jkochavi/Fluid-Power-Controller/wiki_Support_Files/16bitMon.png

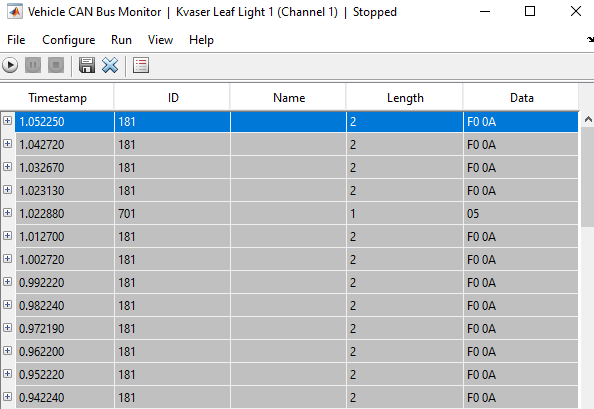
wiki_Support_Files/16bitMon.png
