jkochavi/Fluid-Power-Controller/wiki_Support_Files/16bitSend.png

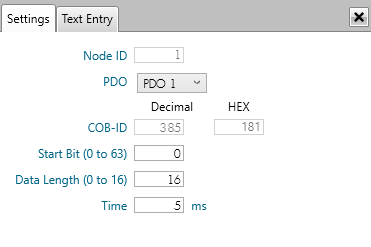
wiki_Support_Files/16bitSend.png
