jkochavi/Fluid-Power-Controller/wiki_Support_Files/CANopenframe.png

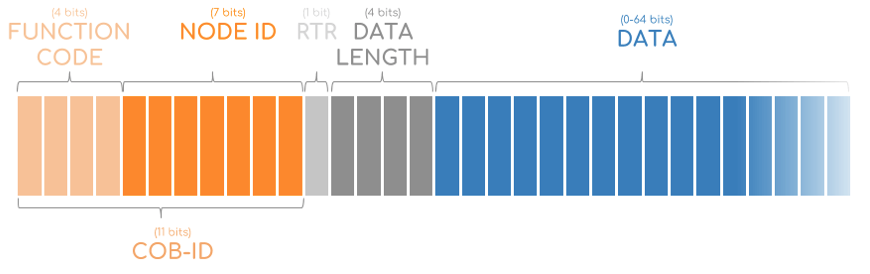
wiki_Support_Files/CANopenframe.png
