jkochavi/Fluid-Power-Controller/wiki_Support_Files/DB9.png

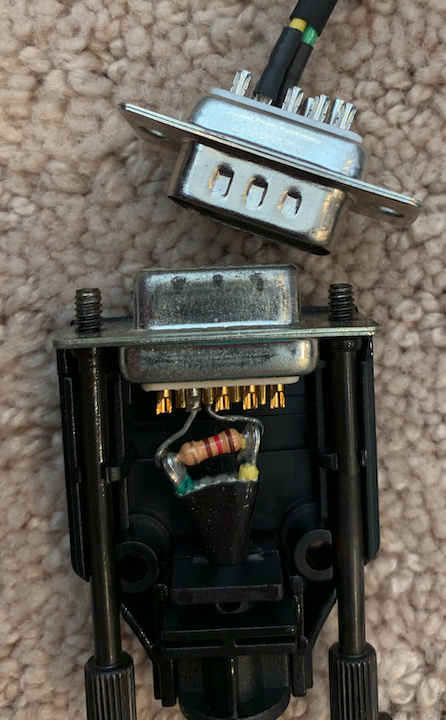
wiki_Support_Files/DB9.png
