jkochavi/Fluid-Power-Controller/wiki_Support_Files/dx.png

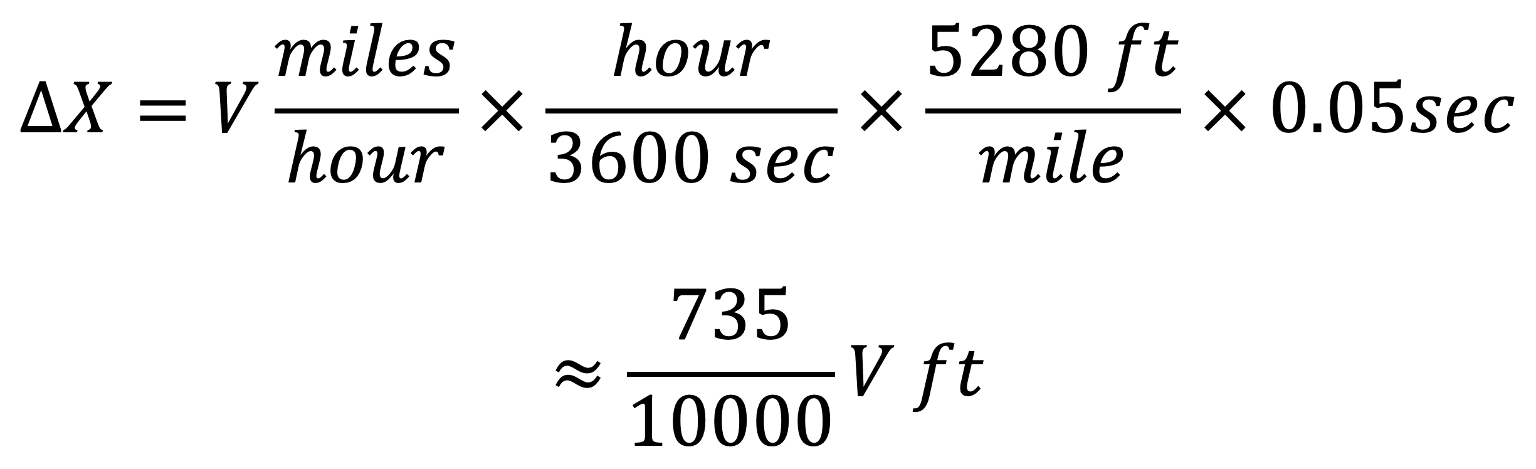
wiki_Support_Files/dx.png
