jkochavi/Fluid-Power-Controller/wiki_Support_Files/fig1.png

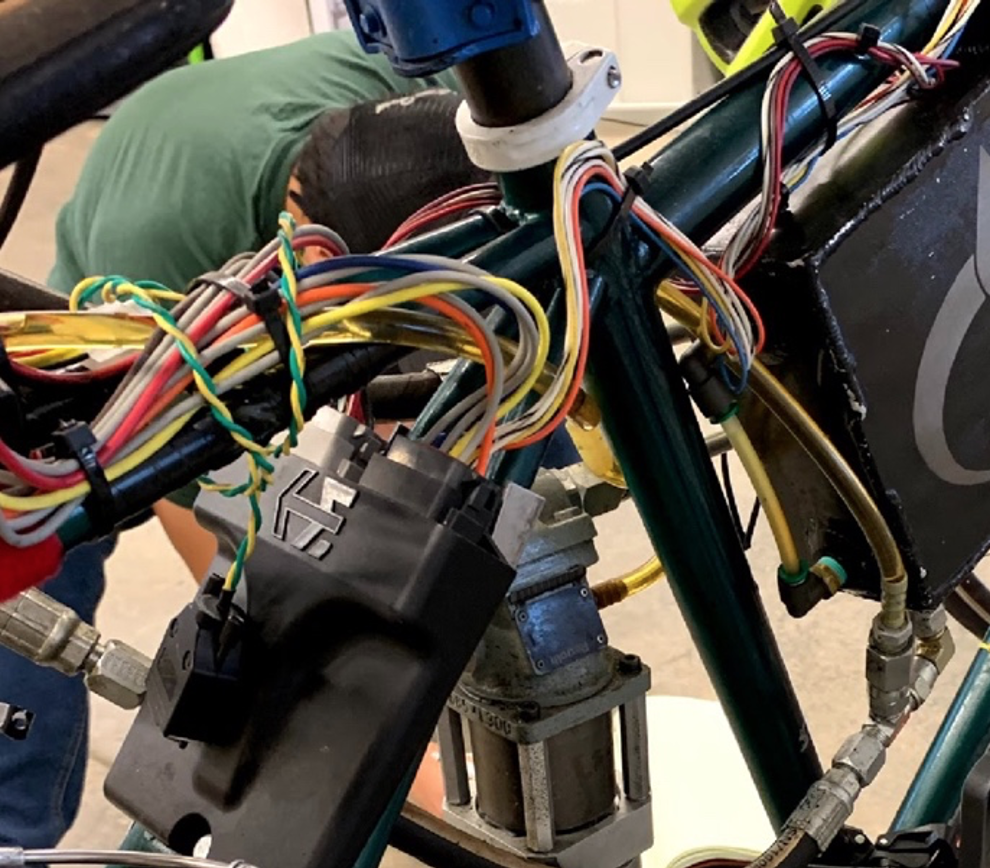
wiki_Support_Files/fig1.png
