jkochavi/Fluid-Power-Controller/wiki_Support_Files/fig2.png

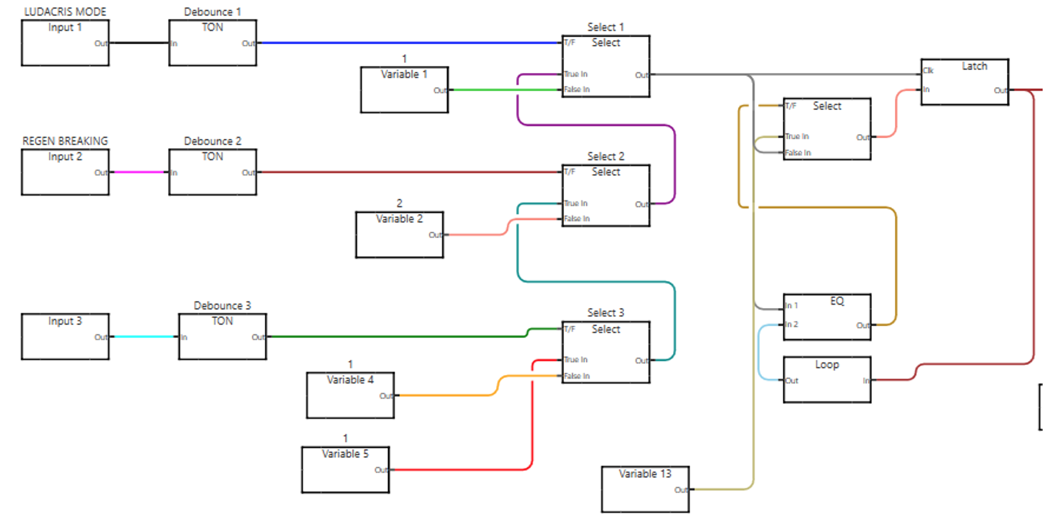
wiki_Support_Files/fig2.png
