jkochavi/Fluid-Power-Controller/wiki_Support_Files/fig3.png

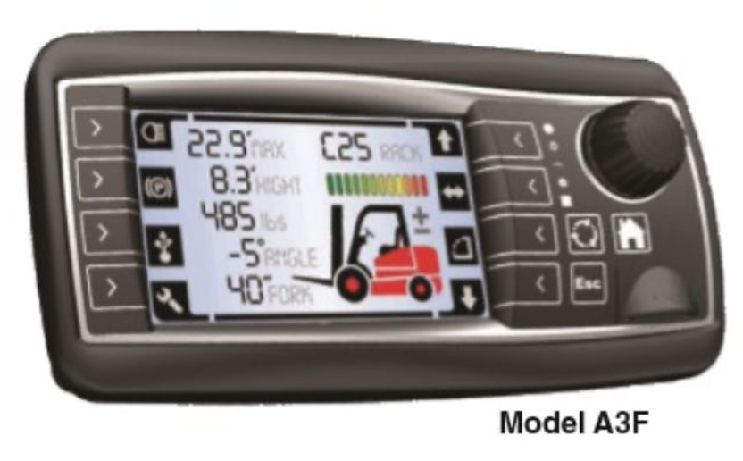
wiki_Support_Files/fig3.png
