jkochavi/Fluid-Power-Controller/wiki_Support_Files/fig4.png

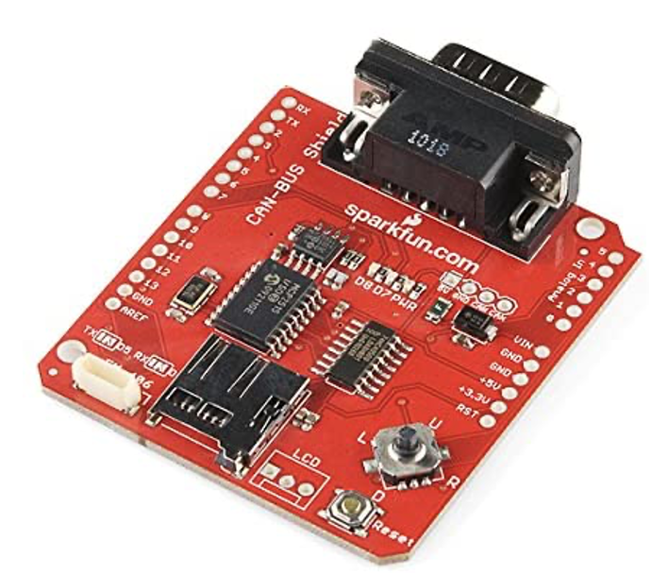
wiki_Support_Files/fig4.png
