jkochavi/Fluid-Power-Controller/wiki_Support_Files/fig5.png

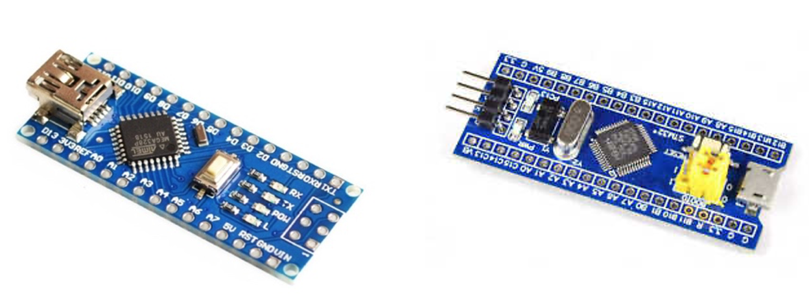
wiki_Support_Files/fig5.png
