jkochavi/Fluid-Power-Controller/wiki_Support_Files/fig6.png

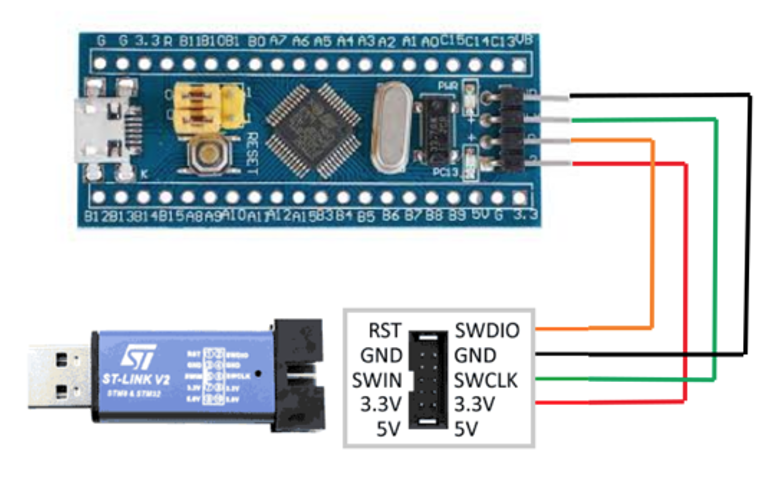
wiki_Support_Files/fig6.png
