jkochavi/Fluid-Power-Controller/wiki_Support_Files/fig7.png

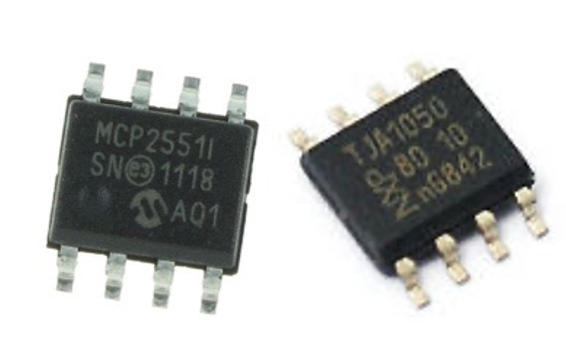
wiki_Support_Files/fig7.png
