jkochavi/Fluid-Power-Controller/wiki_Support_Files/fig8.png

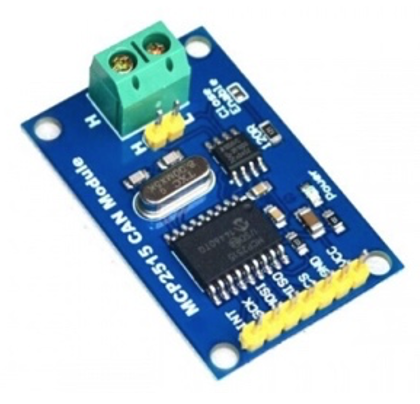
wiki_Support_Files/fig8.png
