jkochavi/Fluid-Power-Controller/wiki_Support_Files/fig9.png

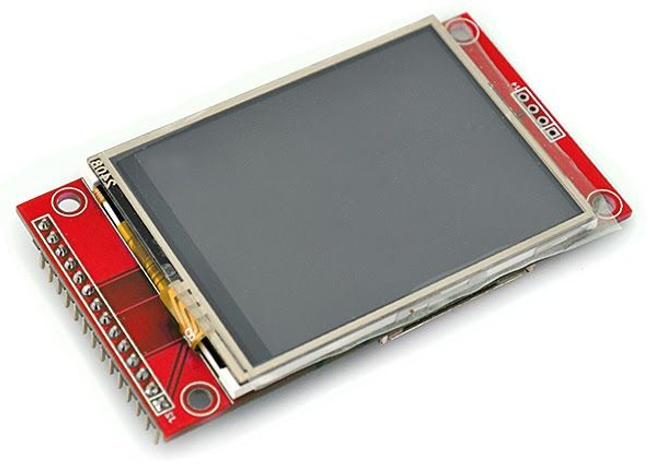
wiki_Support_Files/fig9.png
