jkochavi/Fluid-Power-Controller/wiki_Support_Files/fig10.png

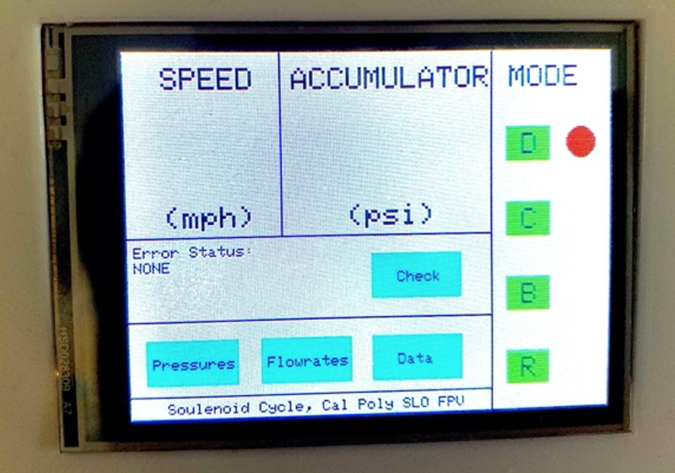
wiki_Support_Files/fig10.png
