jkochavi/Fluid-Power-Controller/wiki_Support_Files/fig11.png

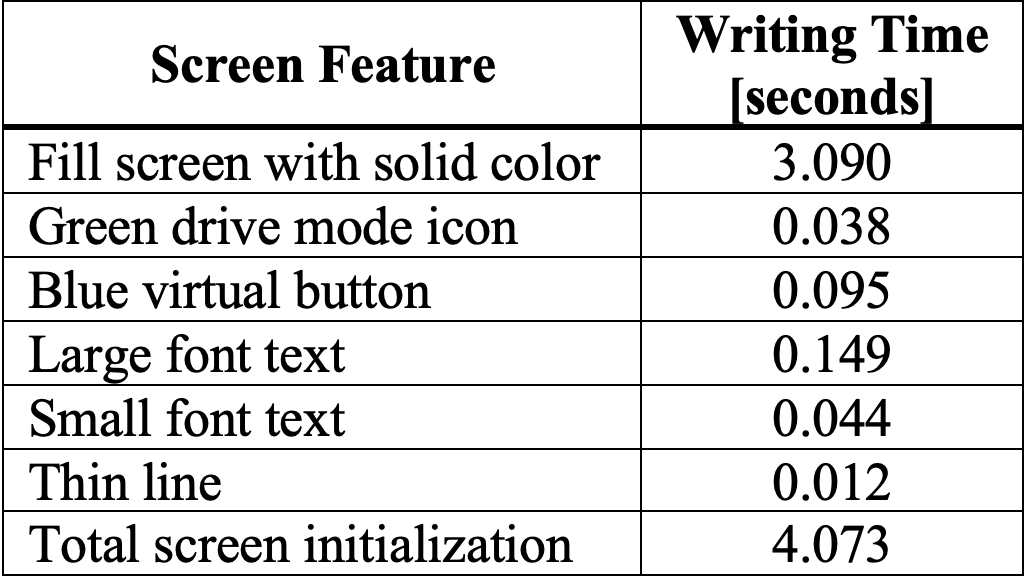
wiki_Support_Files/fig11.png
