jkochavi/Fluid-Power-Controller/wiki_Support_Files/fig12.png

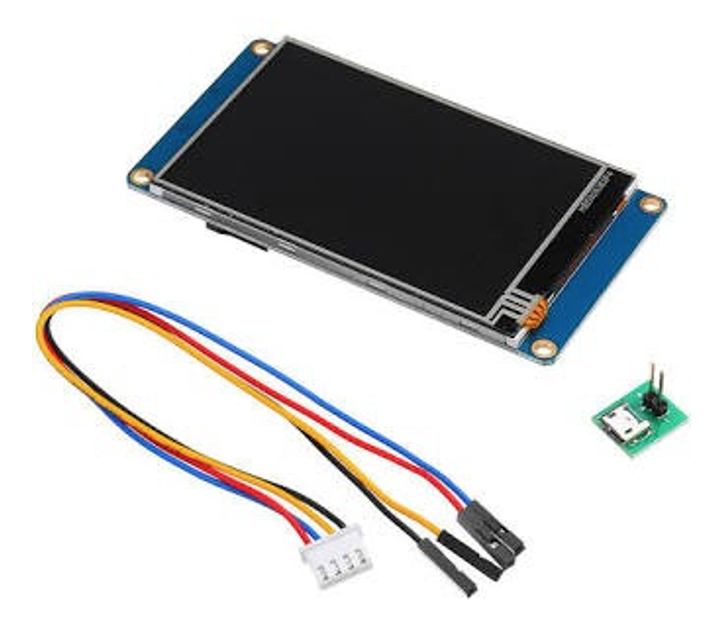
wiki_Support_Files/fig12.png
