jkochavi/Fluid-Power-Controller/wiki_Support_Files/fig13.png

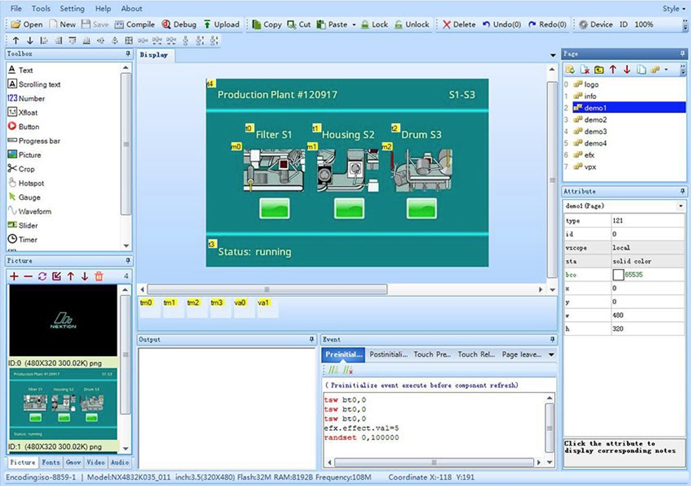
wiki_Support_Files/fig13.png
