jkochavi/Fluid-Power-Controller/wiki_Support_Files/fig14.png

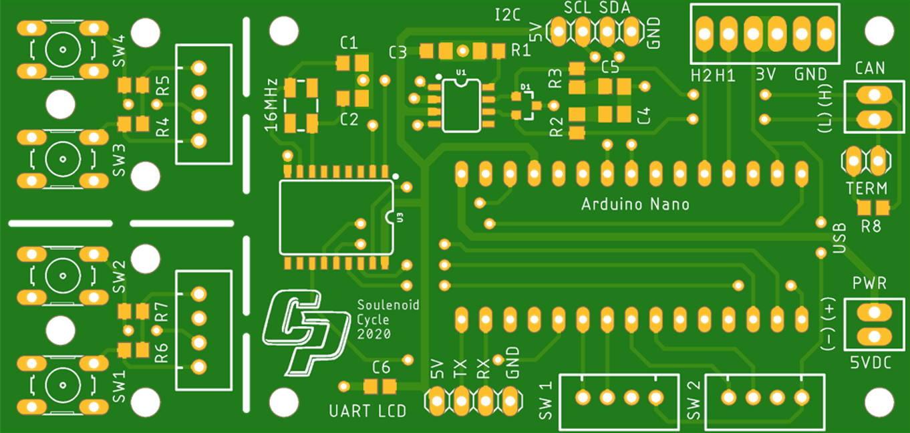
wiki_Support_Files/fig14.png
