jkochavi/Fluid-Power-Controller/wiki_Support_Files/fig15.png

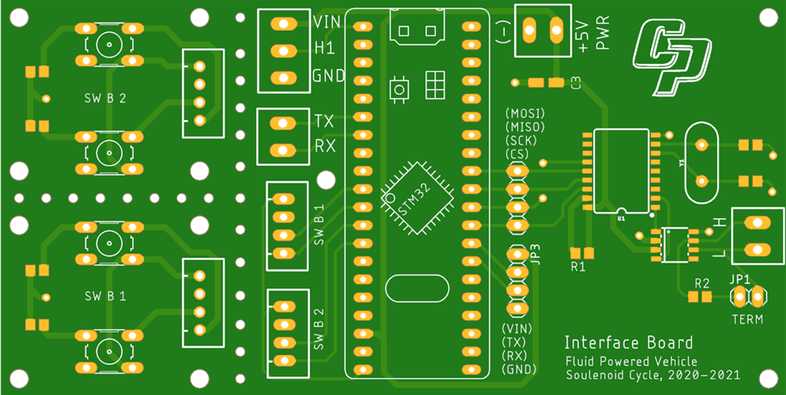
wiki_Support_Files/fig15.png
