jkochavi/Fluid-Power-Controller/wiki_Support_Files/fig16.png

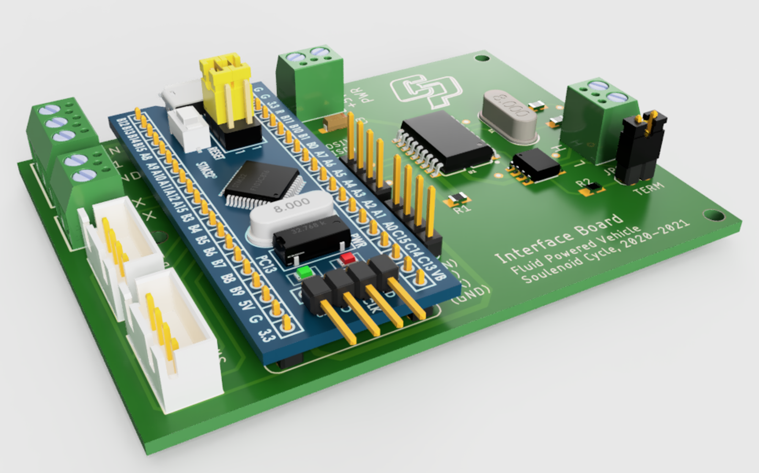
wiki_Support_Files/fig16.png
