jkochavi/Fluid-Power-Controller/wiki_Support_Files/fig17.png

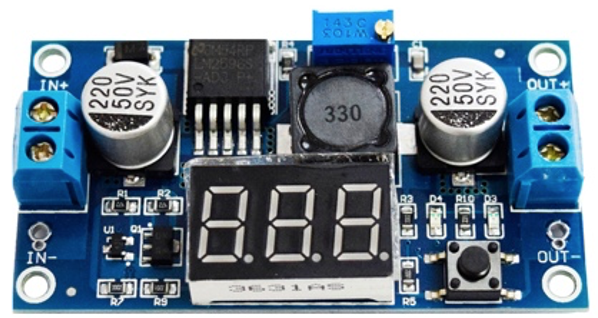
wiki_Support_Files/fig17.png
