jkochavi/Fluid-Power-Controller/wiki_Support_Files/fig18.png

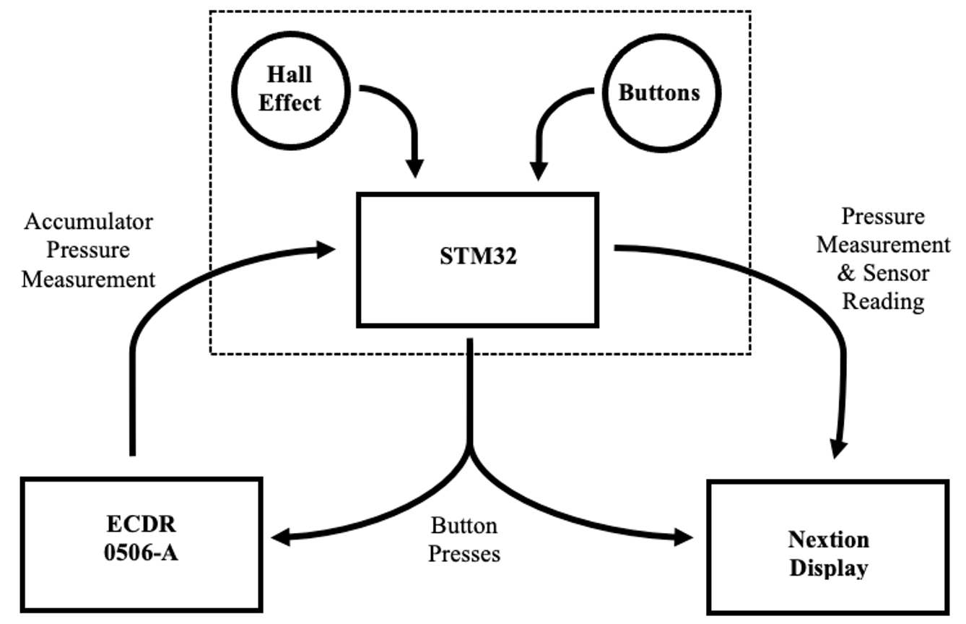
wiki_Support_Files/fig18.png
