jkochavi/Fluid-Power-Controller/wiki_Support_Files/fig19.png

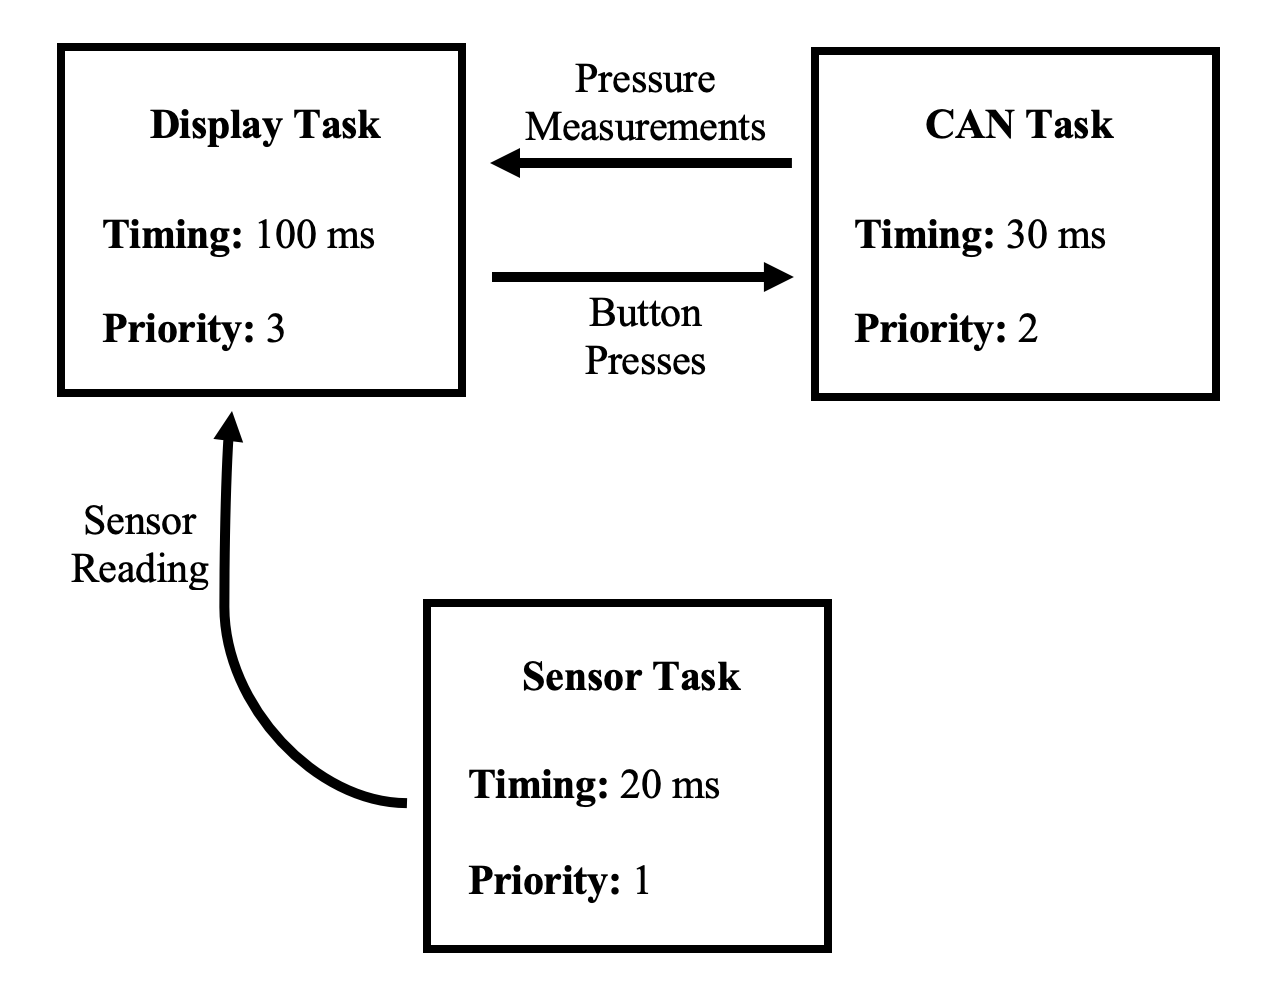
wiki_Support_Files/fig19.png
