jkochavi/Fluid-Power-Controller/wiki_Support_Files/fig20.png

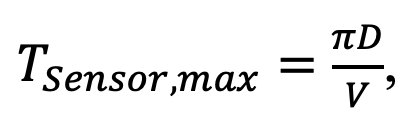
wiki_Support_Files/fig20.png
