jkochavi/Fluid-Power-Controller/wiki_Support_Files/fig22.png

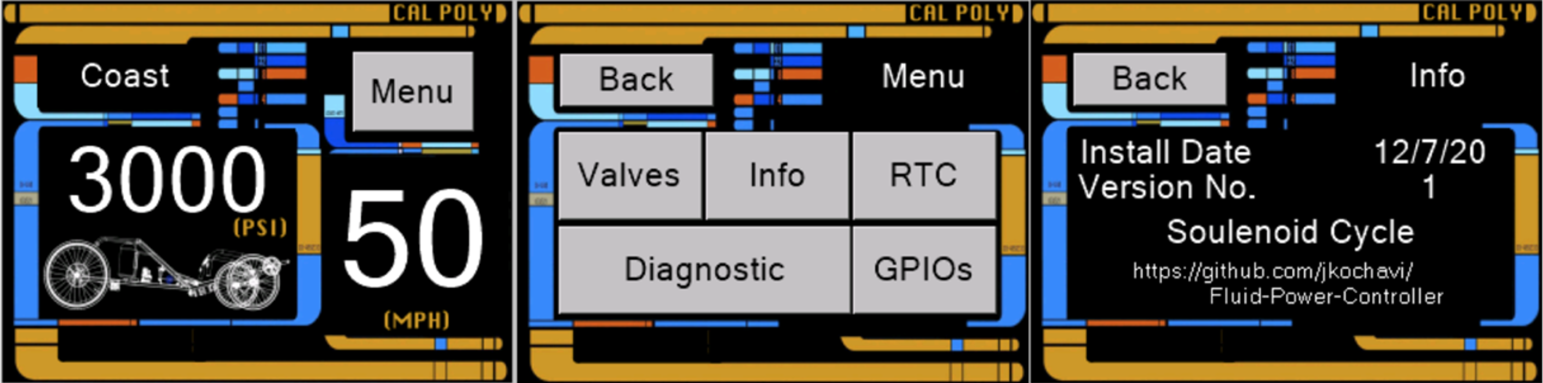
wiki_Support_Files/fig22.png
