jkochavi/Fluid-Power-Controller/wiki_Support_Files/fig23.png

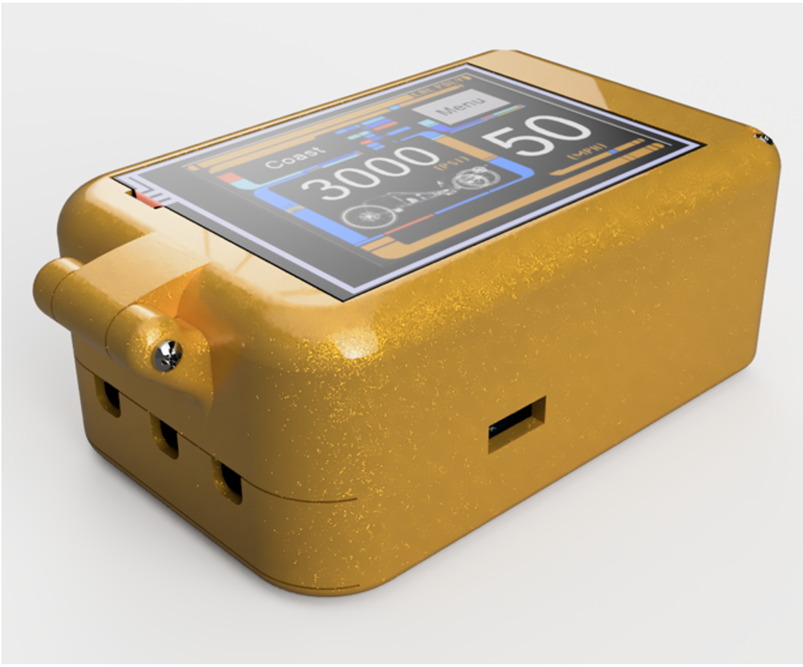
wiki_Support_Files/fig23.png
