jkochavi/Fluid-Power-Controller/wiki_Support_Files/fig24.png

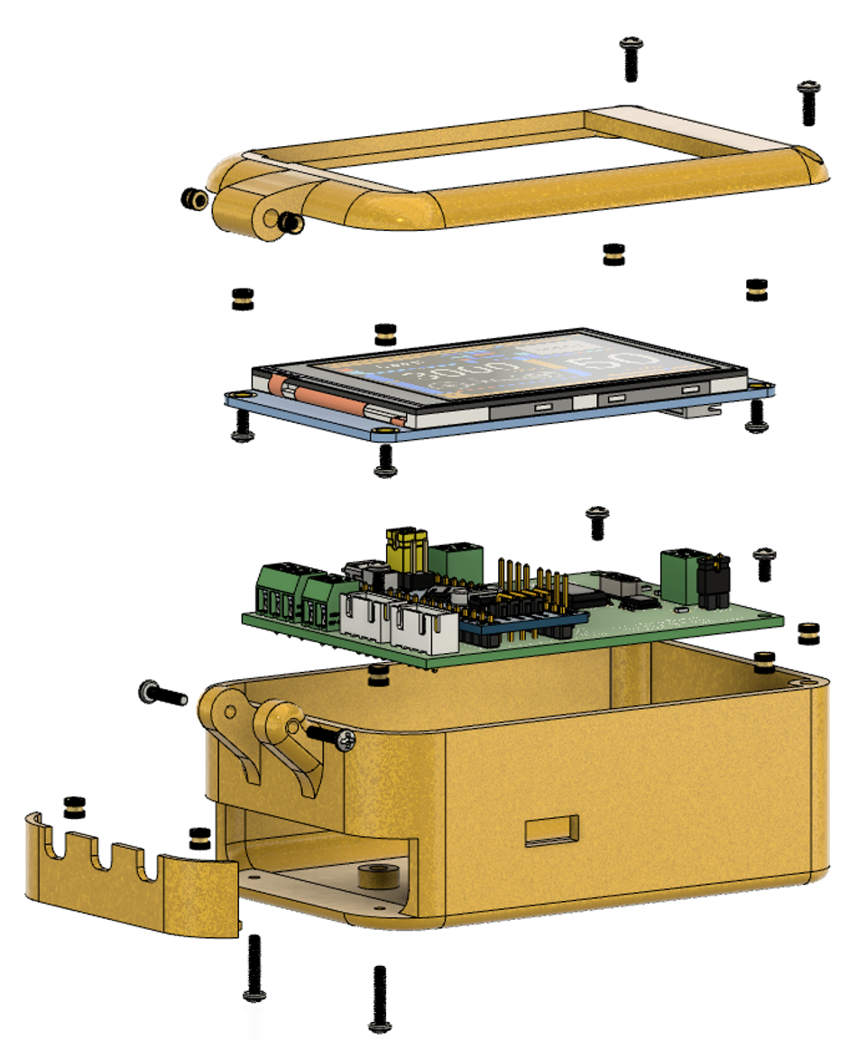
wiki_Support_Files/fig24.png
