jkochavi/Fluid-Power-Controller/wiki_Support_Files/fig25.png

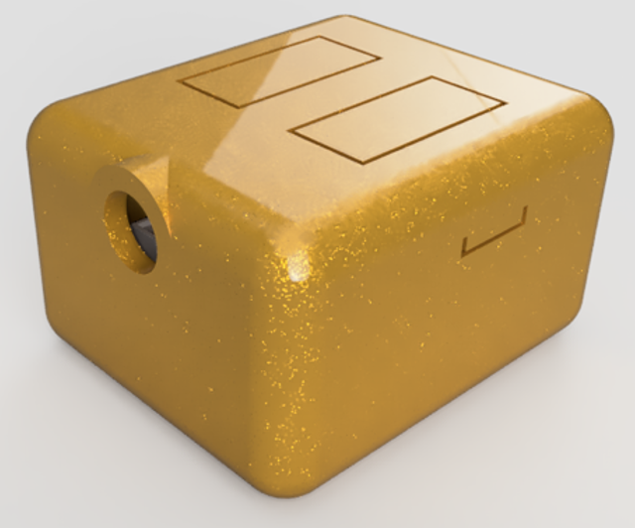
wiki_Support_Files/fig25.png
