jkochavi/Fluid-Power-Controller/wiki_Support_Files/fig26.png

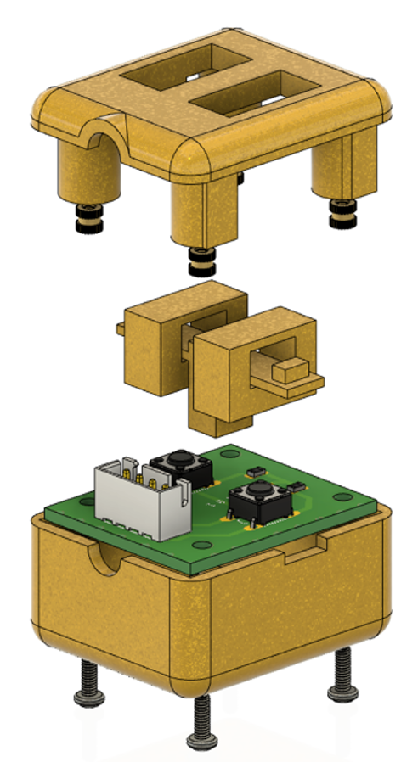
wiki_Support_Files/fig26.png
