jkochavi/Fluid-Power-Controller/wiki_Support_Files/fig27.png

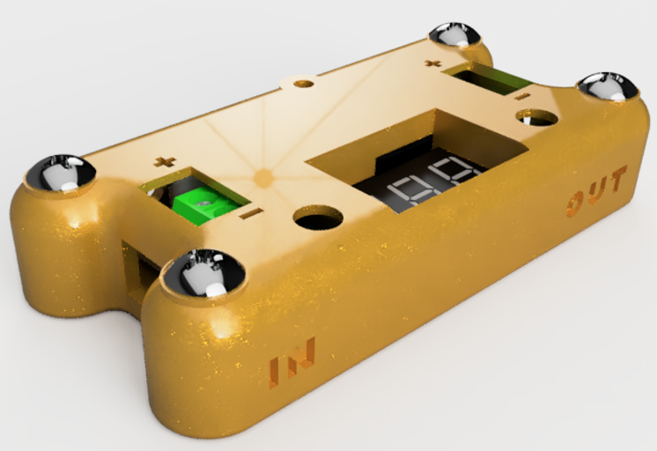
wiki_Support_Files/fig27.png
