jkochavi/Fluid-Power-Controller/wiki_Support_Files/fig28.png

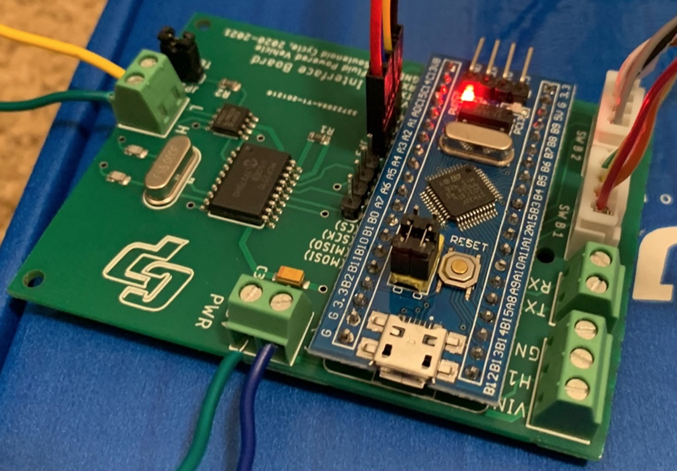
wiki_Support_Files/fig28.png
