jkochavi/Fluid-Power-Controller/wiki_Support_Files/fig29.png

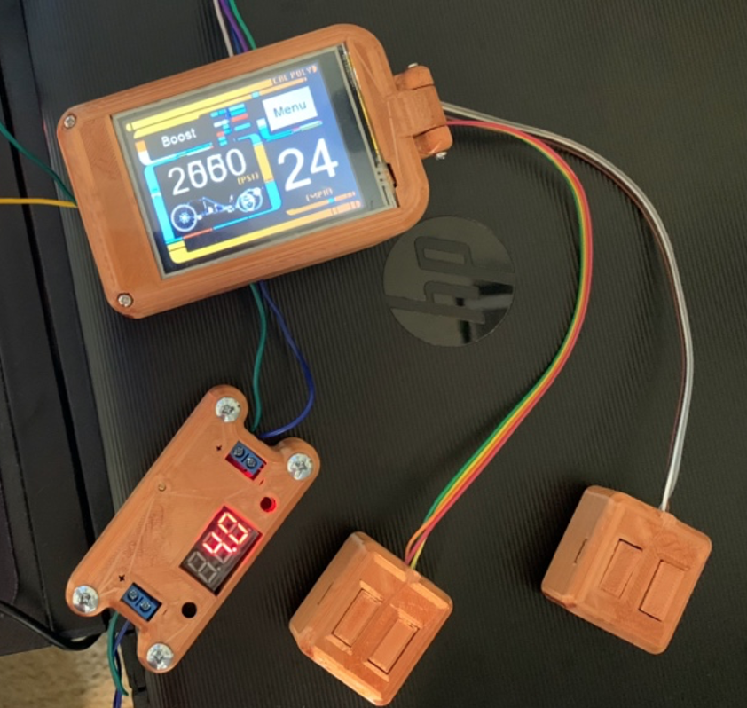
wiki_Support_Files/fig29.png
