jkochavi/Fluid-Power-Controller/wiki_Support_Files/fig30.png

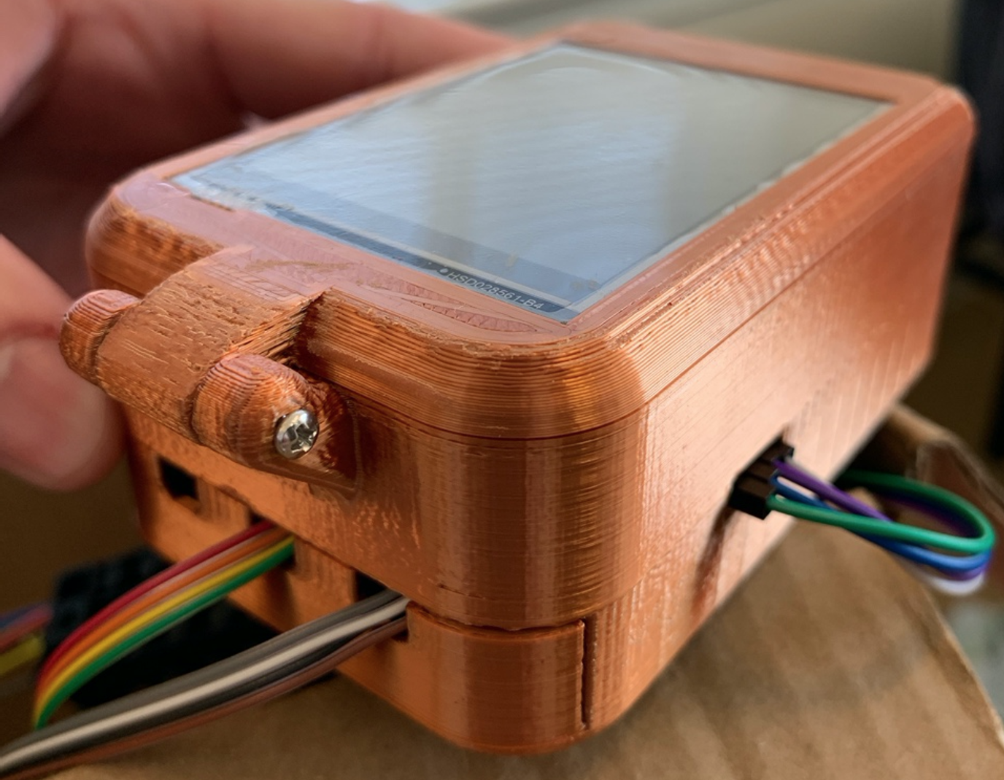
wiki_Support_Files/fig30.png
