jkochavi/Fluid-Power-Controller/wiki_Support_Files/fsm.png

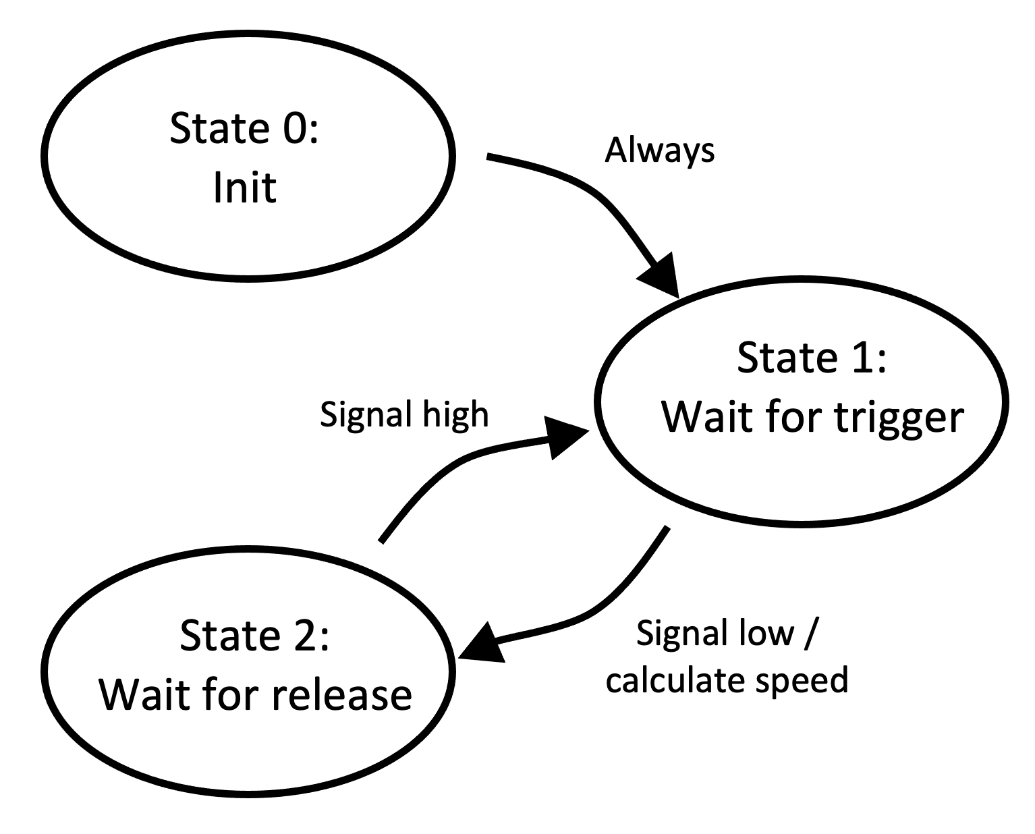
wiki_Support_Files/fsm.png
