jkochavi/Fluid-Power-Controller/wiki_Support_Files/handlebar.png

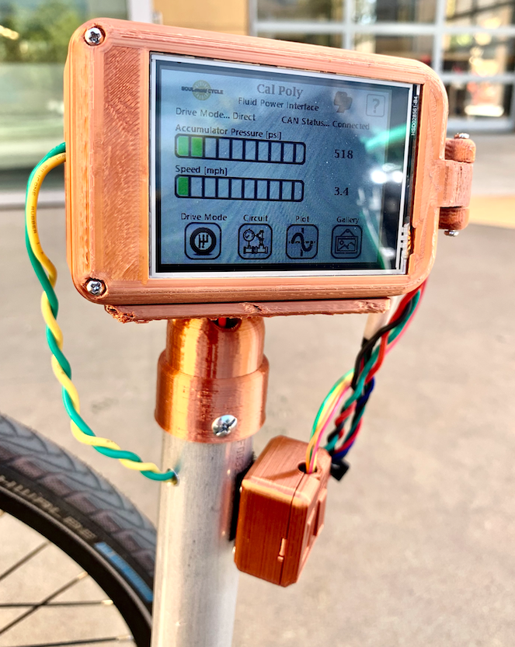
wiki_Support_Files/handlebar.png
