jkochavi/Fluid-Power-Controller/wiki_Support_Files/new1.PNG

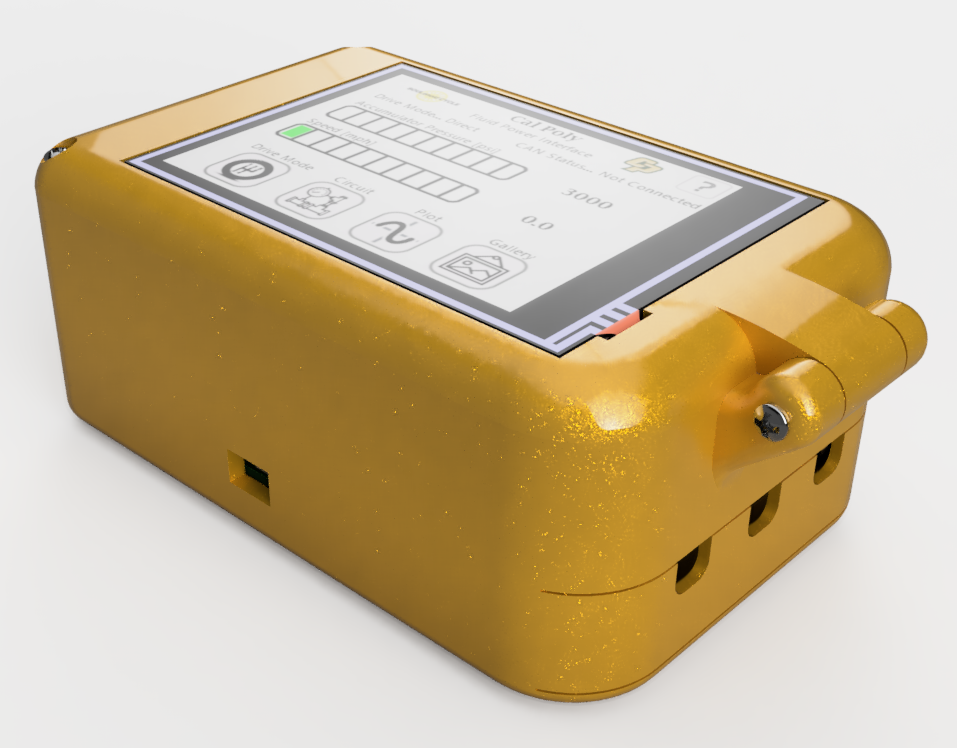
wiki_Support_Files/new1.PNG
