jkochavi/Fluid-Power-Controller/wiki_Support_Files/new2.png

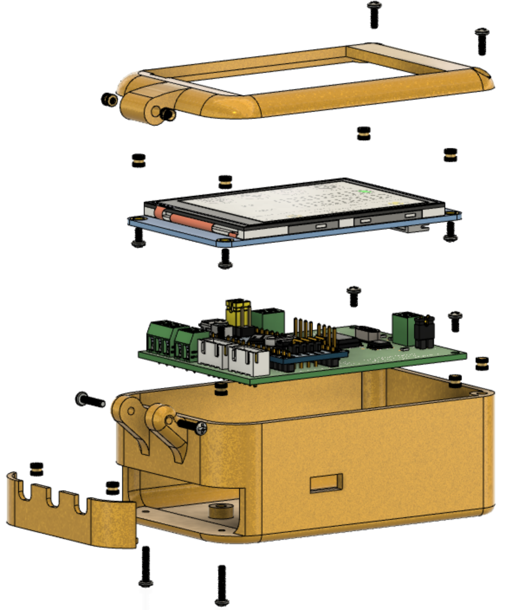
wiki_Support_Files/new2.png
