jkochavi/Fluid-Power-Controller/wiki_Support_Files/Pages.png

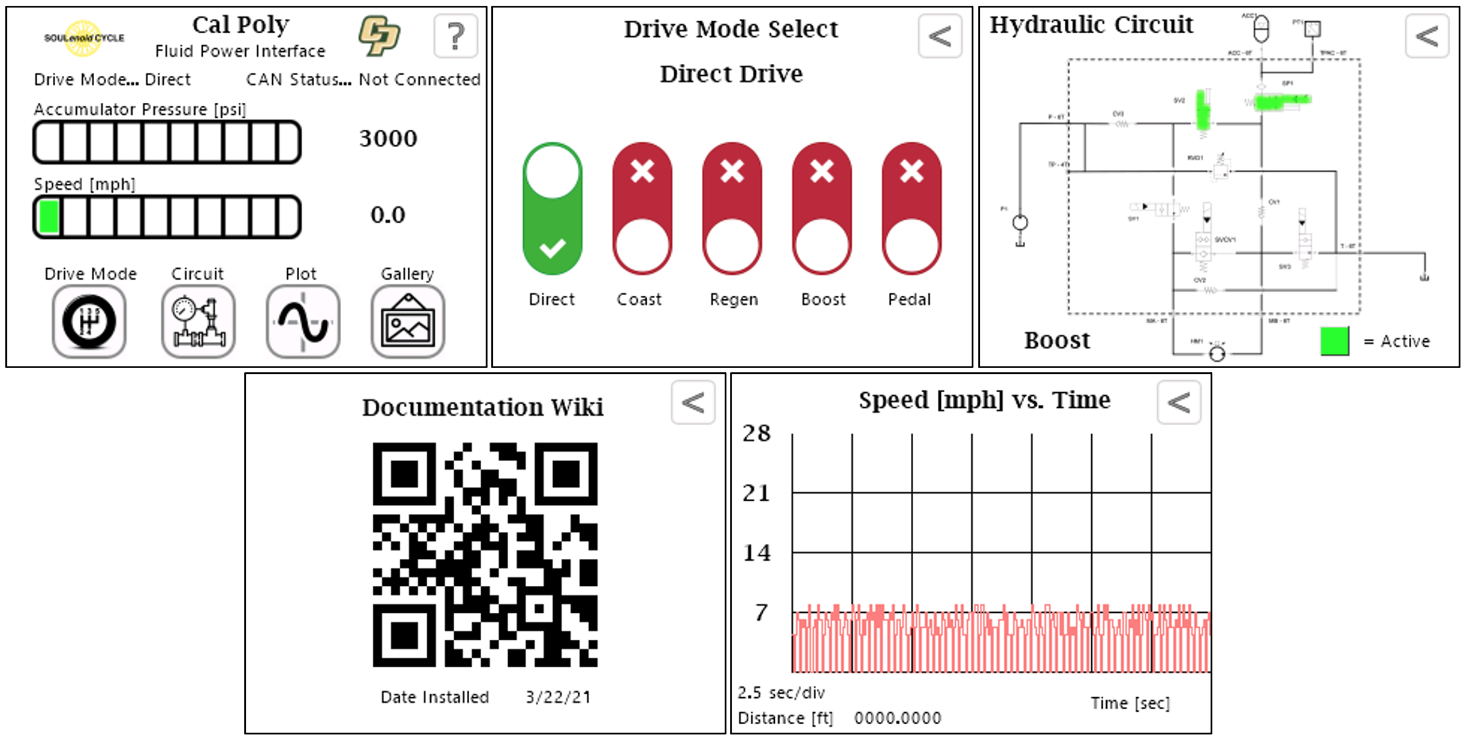
wiki_Support_Files/Pages.png
