jkochavi/Fluid-Power-Controller/wiki_Support_Files/pcbSch.png

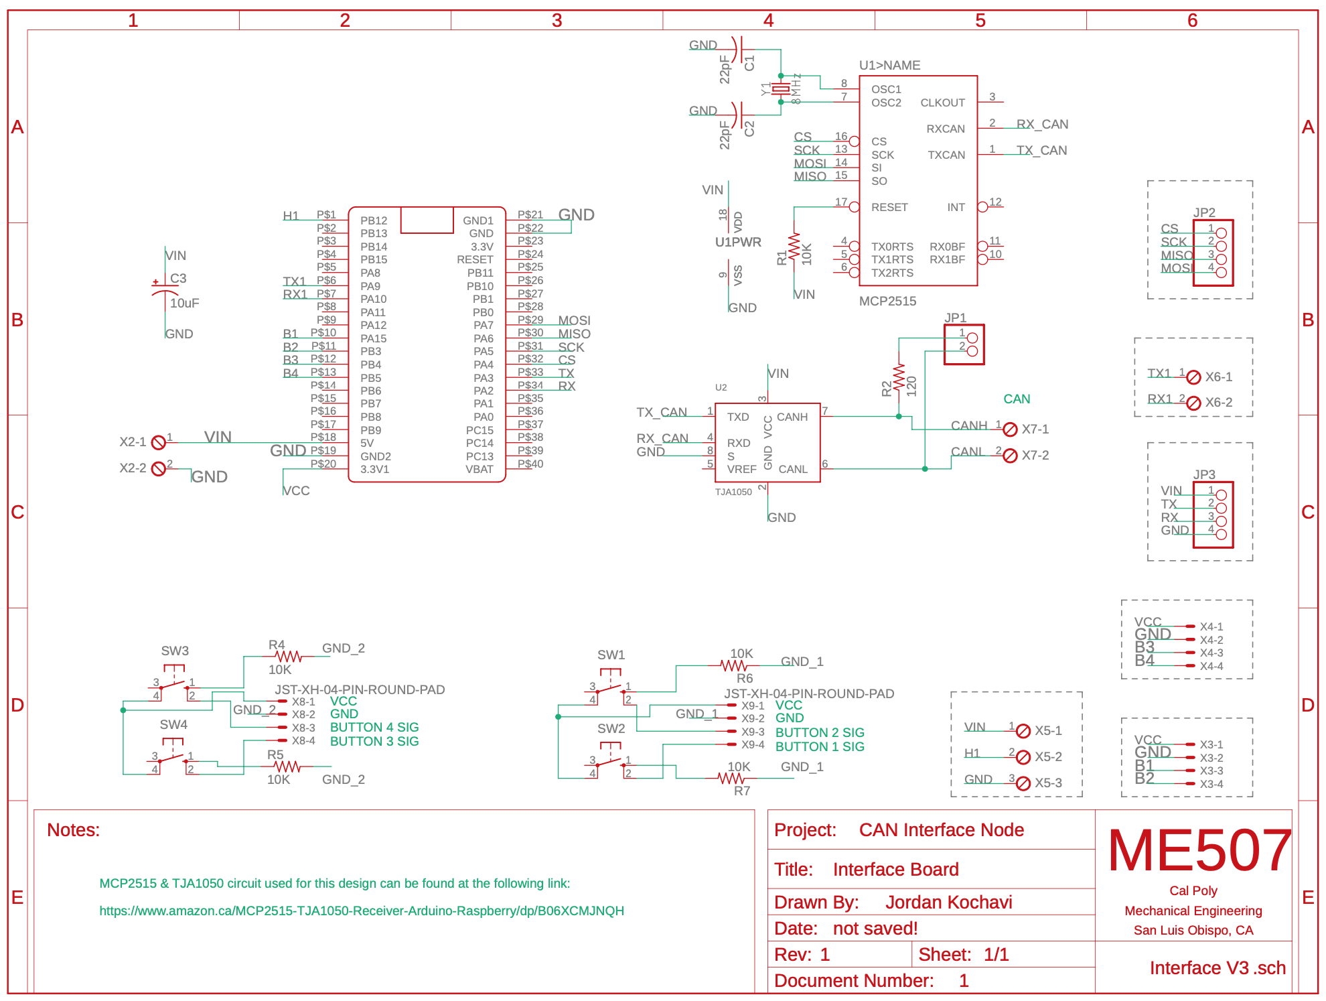
wiki_Support_Files/pcbSch.png
