jkochavi/Fluid-Power-Controller/wiki_Support_Files/PLC.PNG

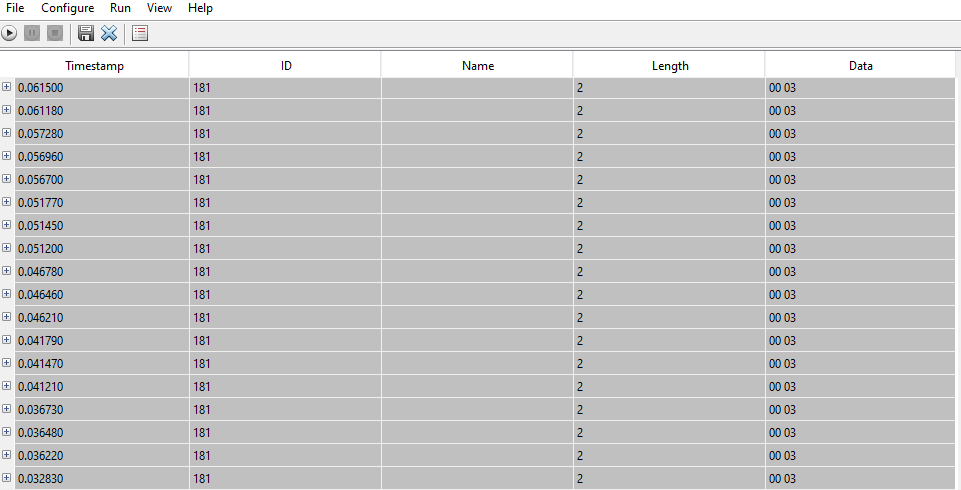
wiki_Support_Files/PLC.PNG
