jkochavi/Fluid-Power-Controller/wiki_Support_Files/PLCprogram2.png

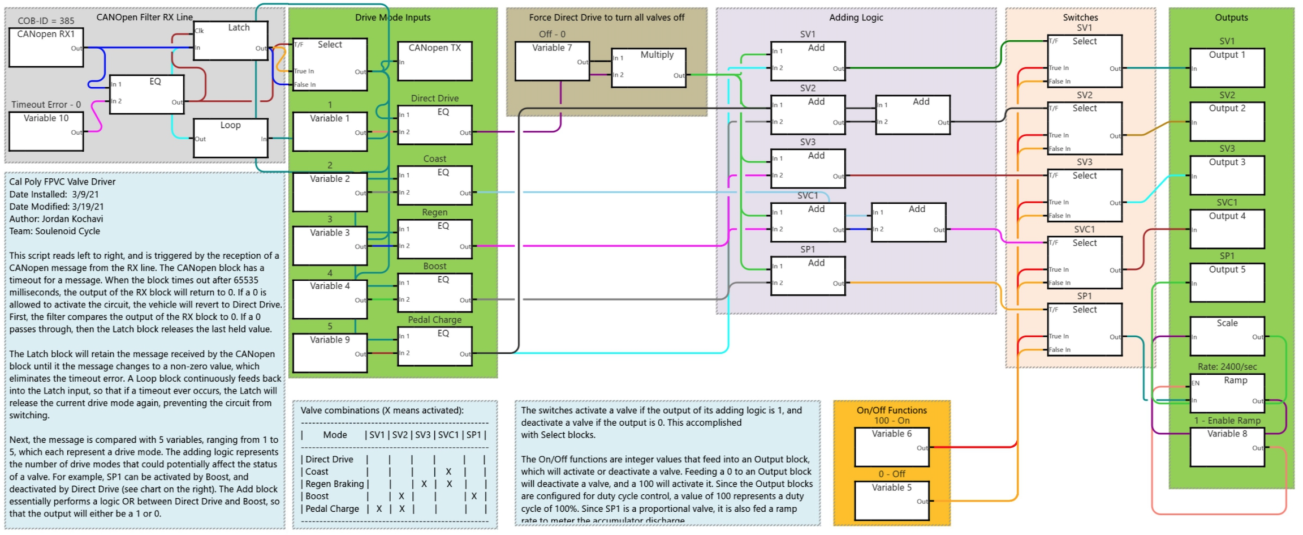
wiki_Support_Files/PLCprogram2.png
