jkochavi/Fluid-Power-Controller/wiki_Support_Files/PLCprogram.png

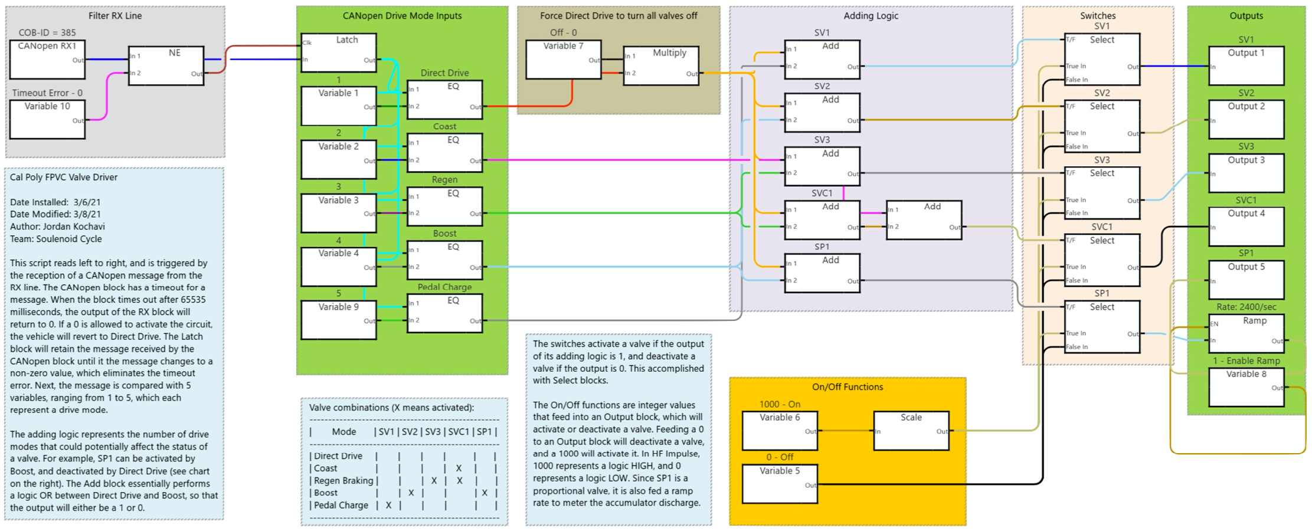
wiki_Support_Files/PLCprogram.png
