jkochavi/Fluid-Power-Controller/wiki_Support_Files/pressureTransducer.png

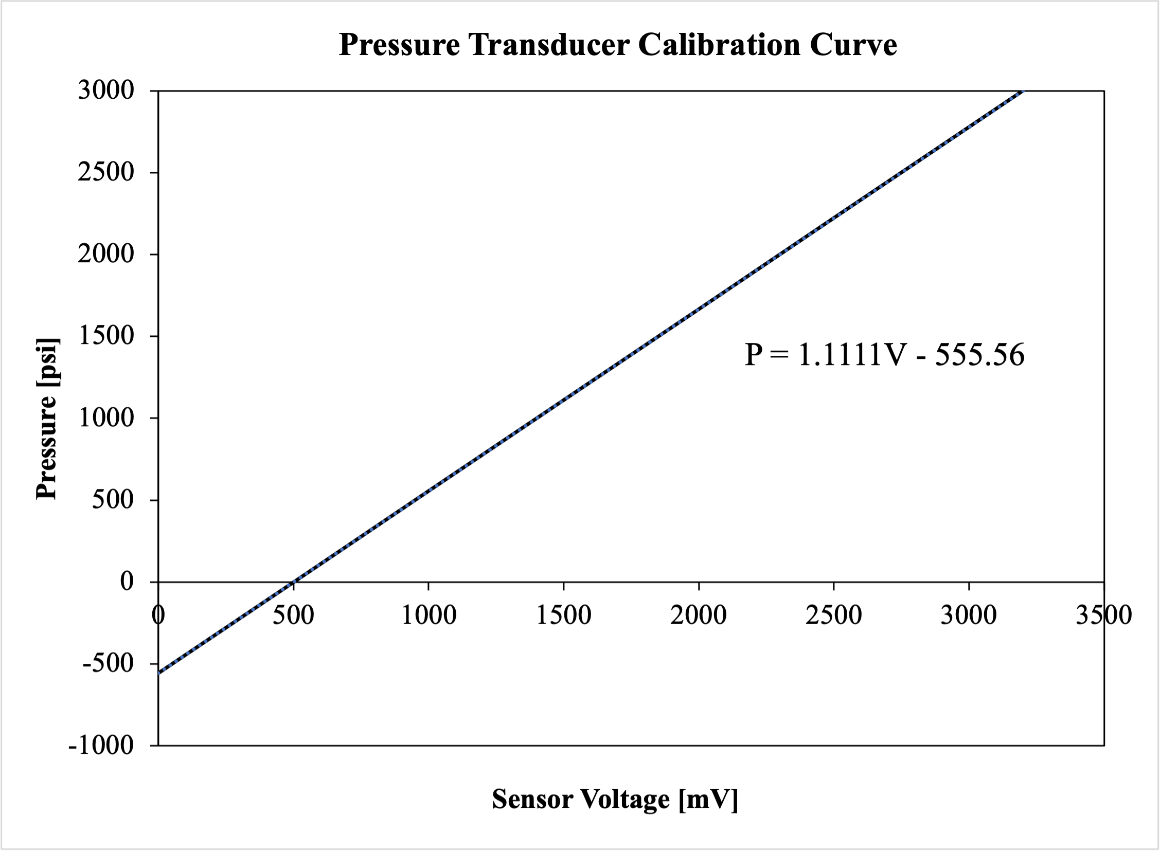
wiki_Support_Files/pressureTransducer.png
