jkochavi/Fluid-Power-Controller/wiki_Support_Files/Program4_3.png

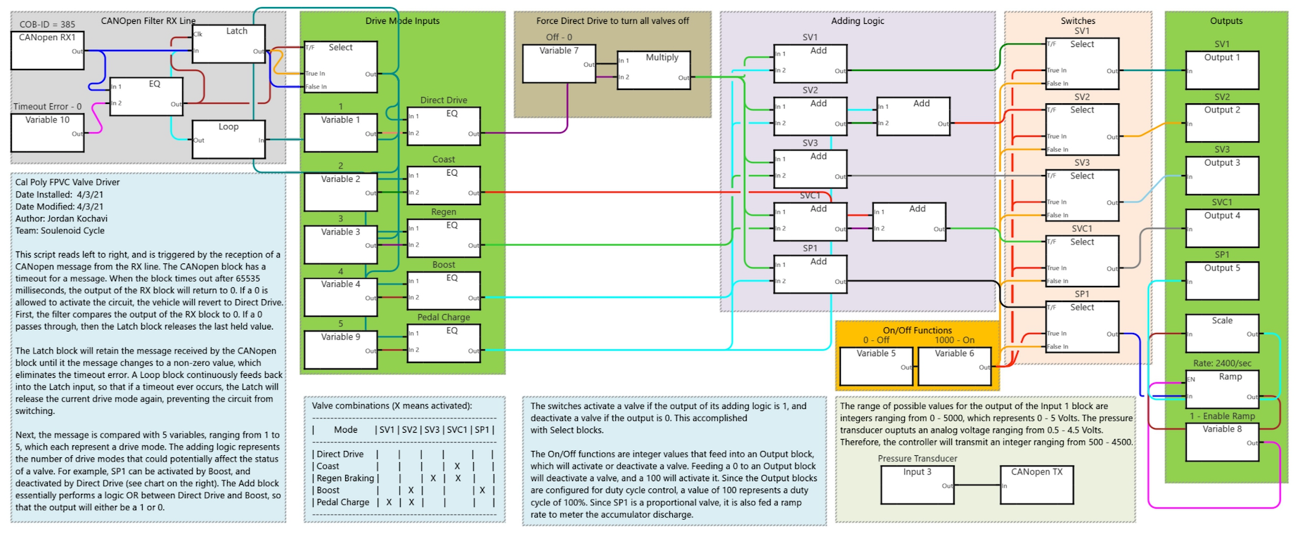
wiki_Support_Files/Program4_3.png
