jkochavi/Fluid-Power-Controller/wiki_Support_Files/Receive_PDO.png

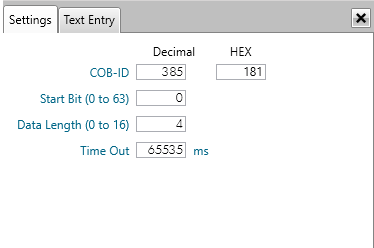
wiki_Support_Files/Receive_PDO.png
