jkochavi/Fluid-Power-Controller/wiki_Support_Files/ScreenStand.png

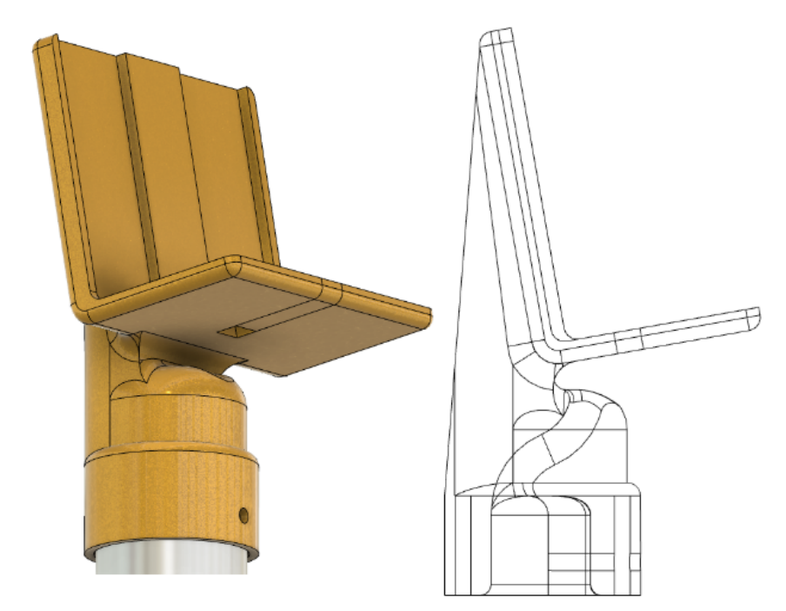
wiki_Support_Files/ScreenStand.png
