jkochavi/Fluid-Power-Controller/wiki_Support_Files/Transmit_PDO.png

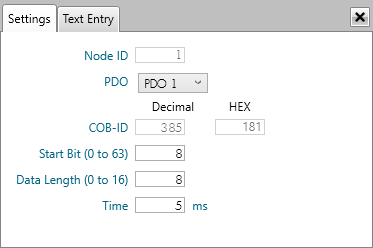
wiki_Support_Files/Transmit_PDO.png
