jkochavi/Fluid-Power-Controller/wiki_Support_Files/ttl.png

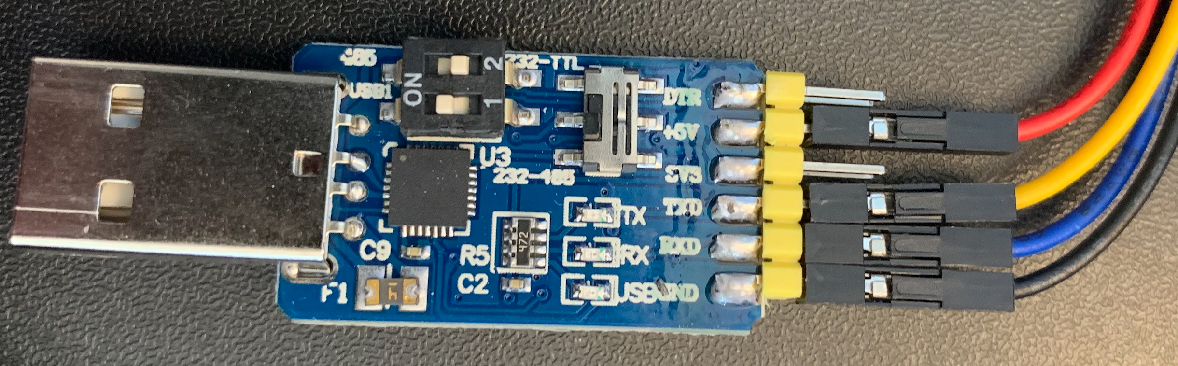
wiki_Support_Files/ttl.png
