jkochavi/Fluid-Power-Controller/wiki_Support_Files/underseat.png

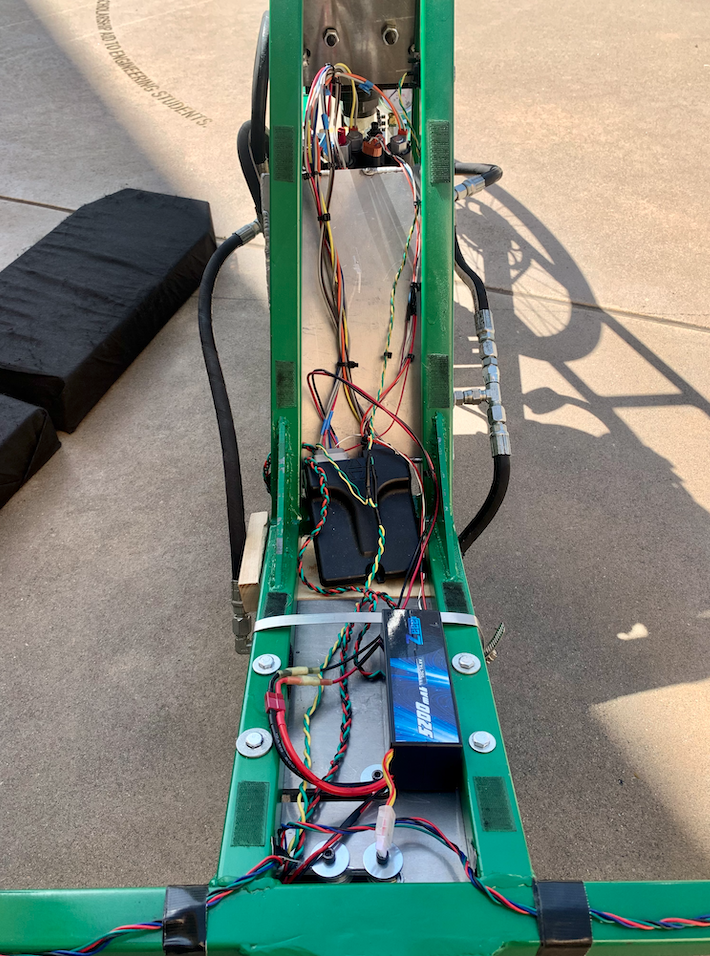
wiki_Support_Files/underseat.png
