jkochavi/Fluid-Power-Controller/wiki_Support_Files/vehicle2.png

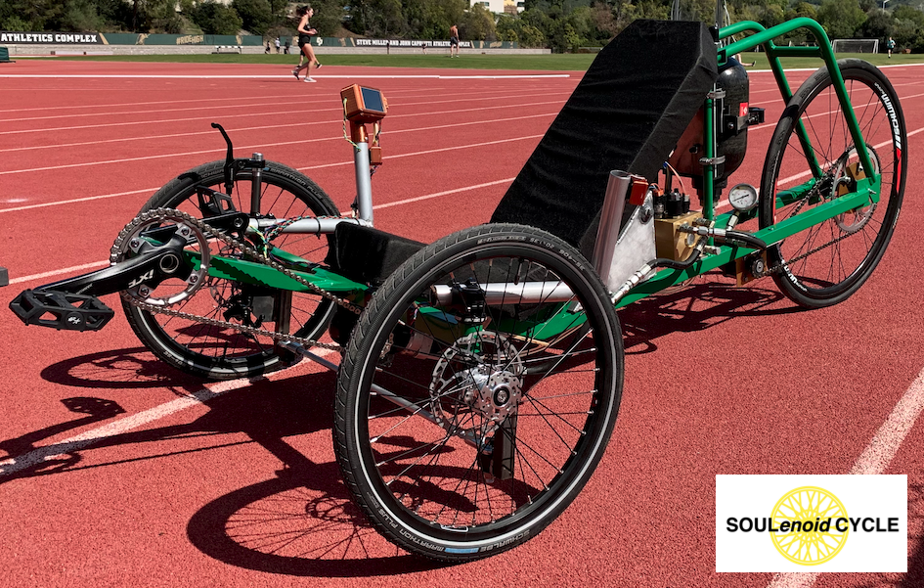
wiki_Support_Files/vehicle2.png
